oresmius/Landell/Arquivos Kicad/Interface_IQ.kicad_sch

## KiCad design Arquivos Kicad/Interface_IQ.kicad_sch (2026-09-18)

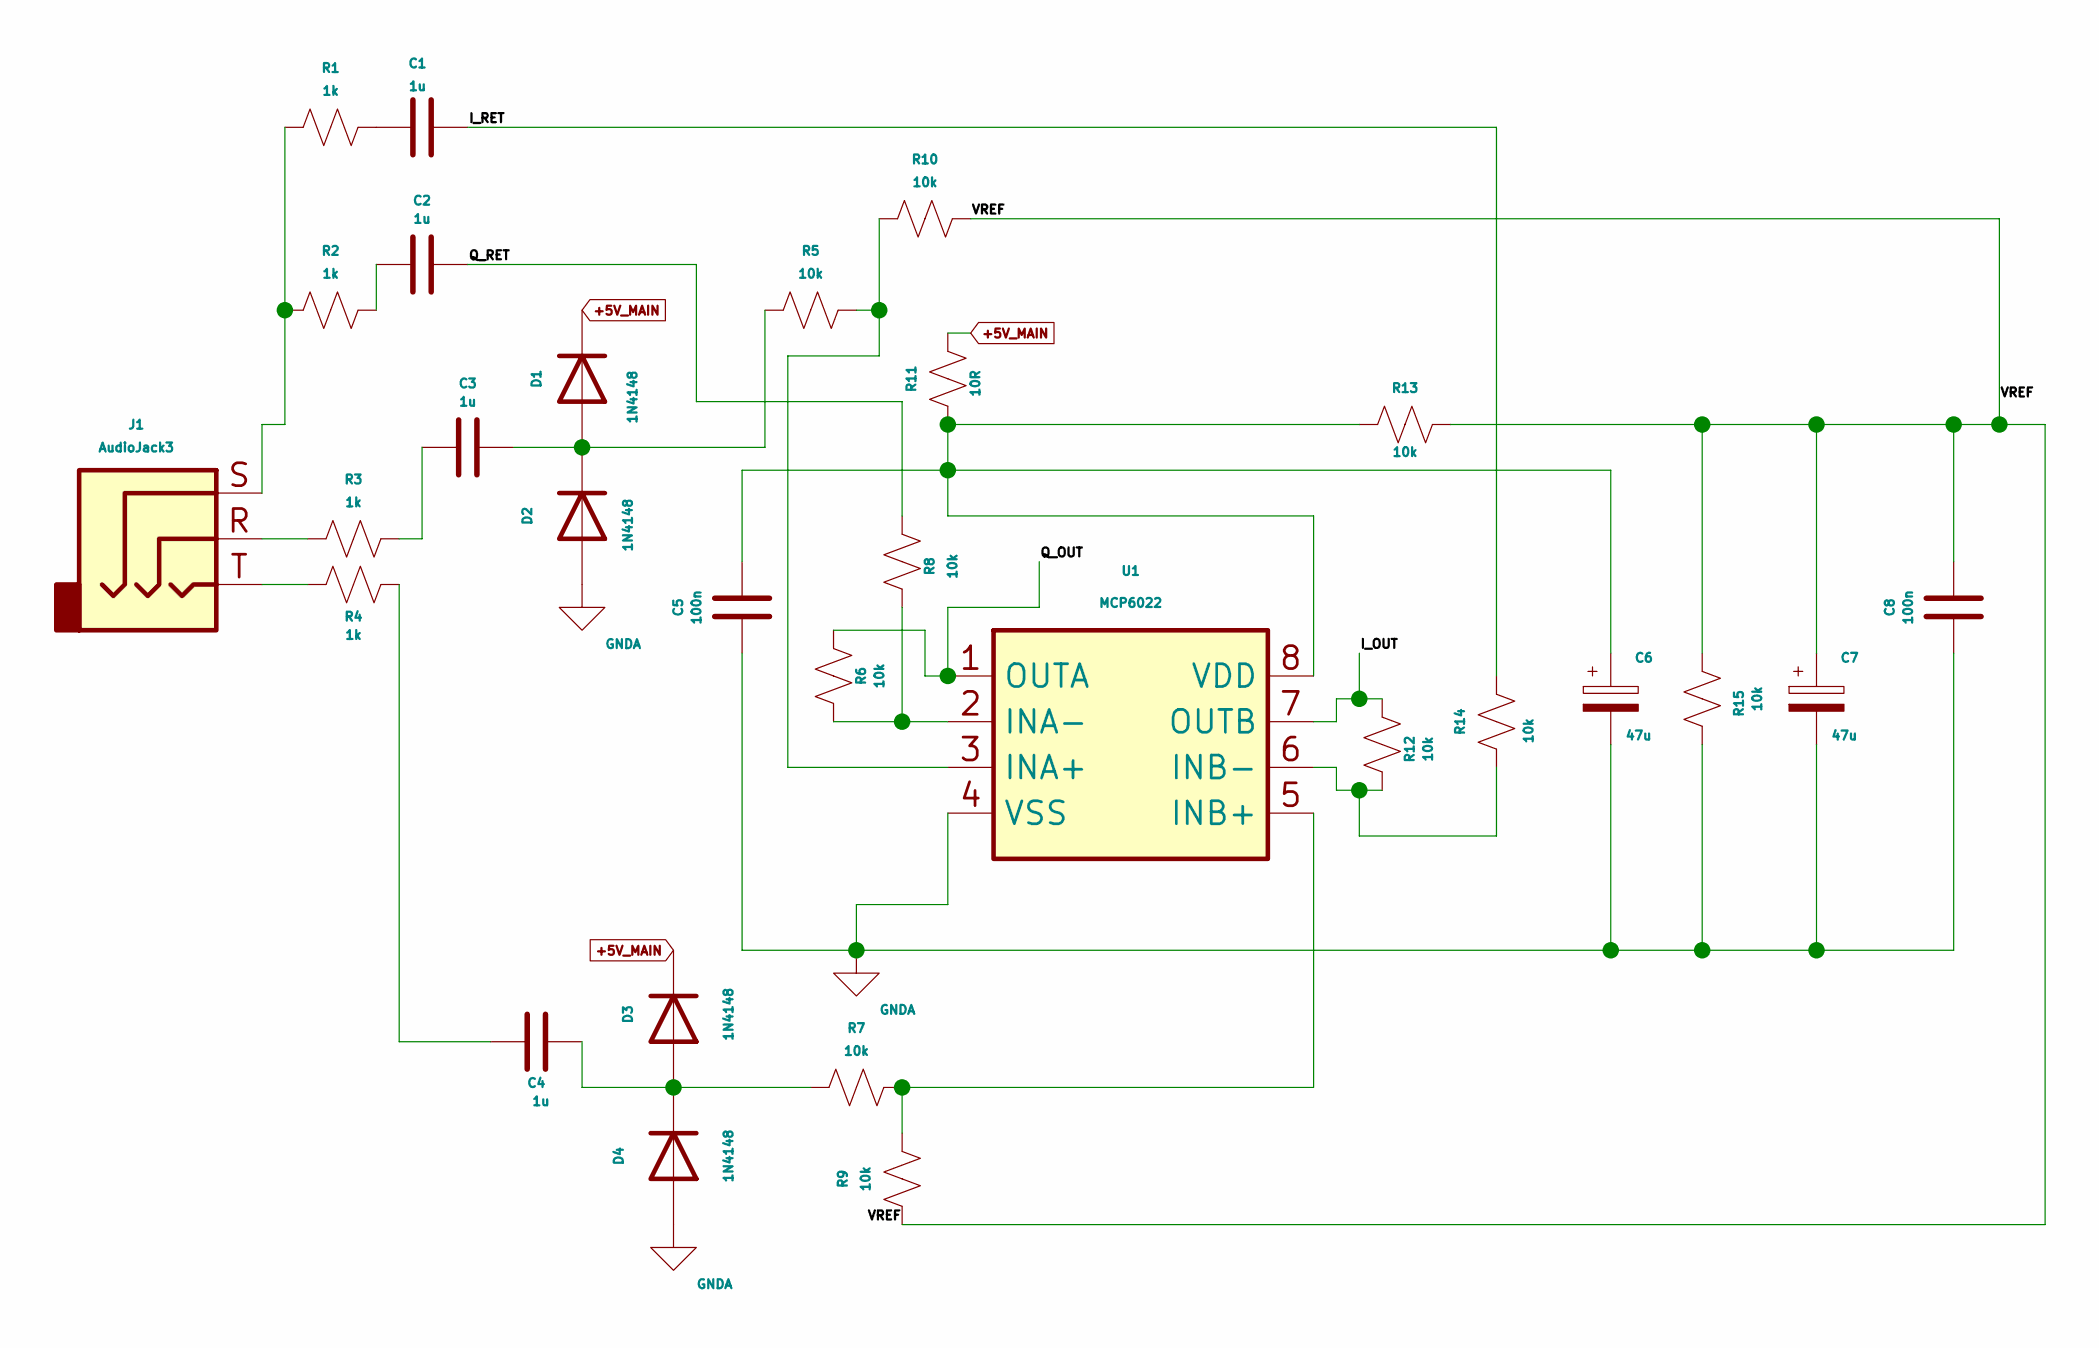
[picture p9: schematic Interface_IQ.kicad_sch]

Parts:
C1, C2, C3, C4: 1u
C5, C8: 100n
C6, C7: 47u; SOIC-8_3.9x4.9mm_P1.27mm
D1, D2, D3, D4: 1N4148; D_DO-35_SOD27_P7.62mm_Horizontal
J1: AudioJack3
R1, R2, R3, R4: 1k
R5, R6, R7, R8, R9, R10, R12, R13, R14, R15: 10k
R11: 10R
U1: MCP6022

Connections:
+5V_MAIN: D1.1 (K), D3.1 (K), R11.1
GNDA: C5.1, C6.2, C7.2, C8.1, D2.2 (A), D4.2 (A), R15.1, U1.4 (VSS)
I_OUT: R12.1, U1.7 (OUTB)
I_RET: C1.2, R14.1
unnamed: C1.1, R1.2
unnamed: C2.1, R2.2
unnamed: C3.1, R3.2
unnamed: C3.2, D1.2 (A), D2.1 (K), R5.1
unnamed: C4.1, R4.2
unnamed: C4.2, D3.2 (A), D4.1 (K), R7.1
unnamed: C5.2, C6.1, R11.2, R13.1, U1.8 (VDD)
unnamed: J1.R, R3.1
unnamed: J1.S, R1.1, R2.1
unnamed: J1.T, R4.1
unnamed: R6.2, R8.2, U1.2 (INA-)
unnamed: R7.2, R9.2, U1.5 (INB+)
unnamed: R5.2, R10.1, U1.3 (INA+)
unnamed: R12.2, R14.2, U1.6 (INB-)
Q_OUT: R6.1, U1.1 (OUTA)
Q_RET: C2.2, R8.1
VREF: C7.1, C8.2, R9.1, R10.2, R13.2, R15.2
